sertkayahuseyin/Solar-Panel-Tracking-the-Sun-with-Two-Axis-Motion/Media/Images/1.jpg

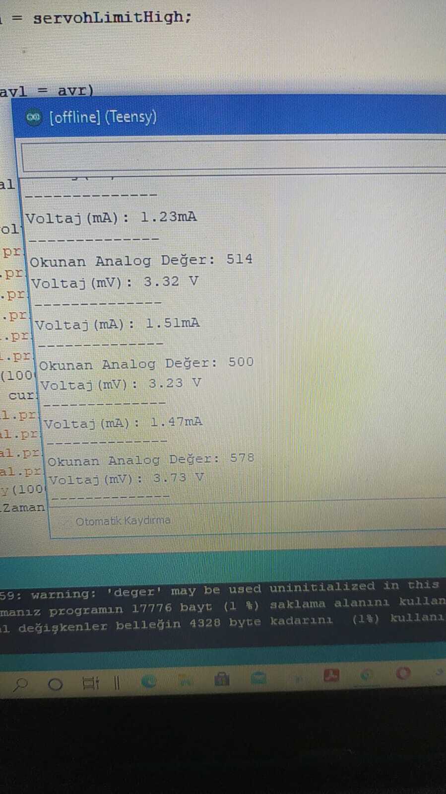
Media/Images/1.jpg
