sertkayahuseyin/Solar-Panel-Tracking-the-Sun-with-Two-Axis-Motion/Media/Images/2.jpg

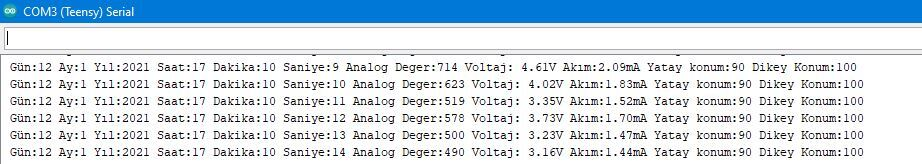
Media/Images/2.jpg
