sertkayahuseyin/Solar-Panel-Tracking-the-Sun-with-Two-Axis-Motion/Media/Images/4.jpg

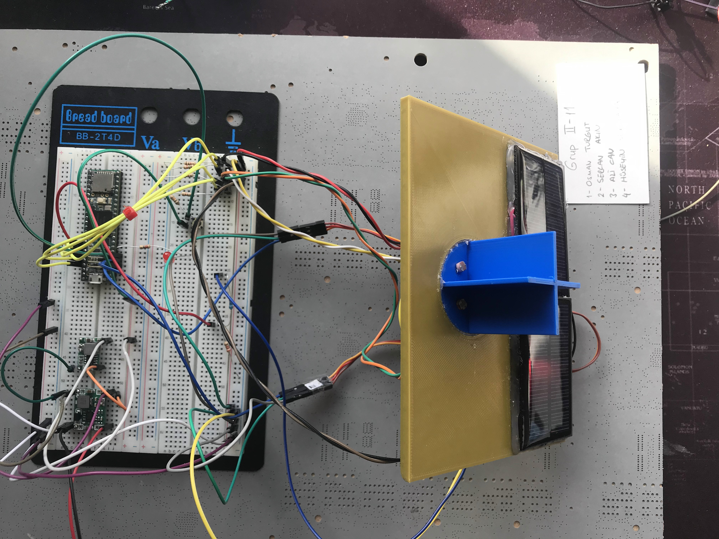
Media/Images/4.jpg
