sertkayahuseyin/Solar-Panel-Tracking-the-Sun-with-Two-Axis-Motion/Media/Images/6.jpg

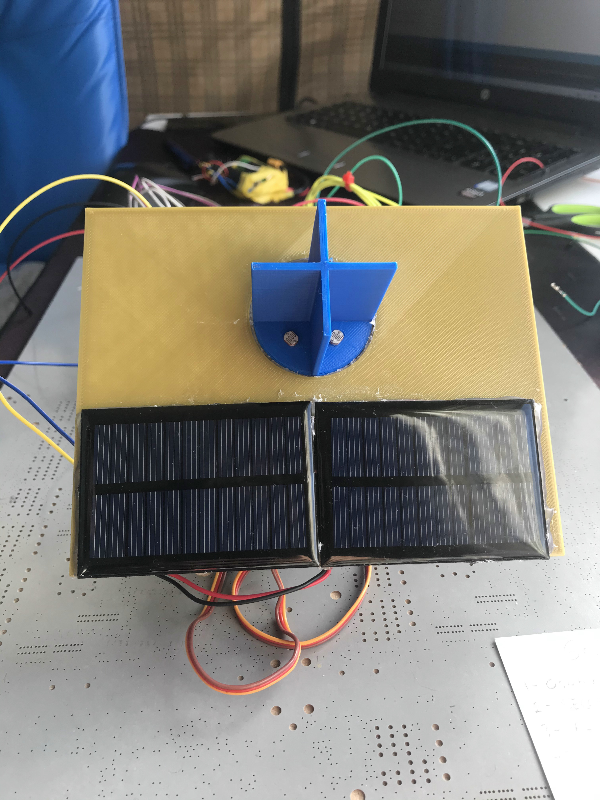
Media/Images/6.jpg
