sertkayahuseyin/Solar-Panel-Tracking-the-Sun-with-Two-Axis-Motion/Media/Images/7.jpg

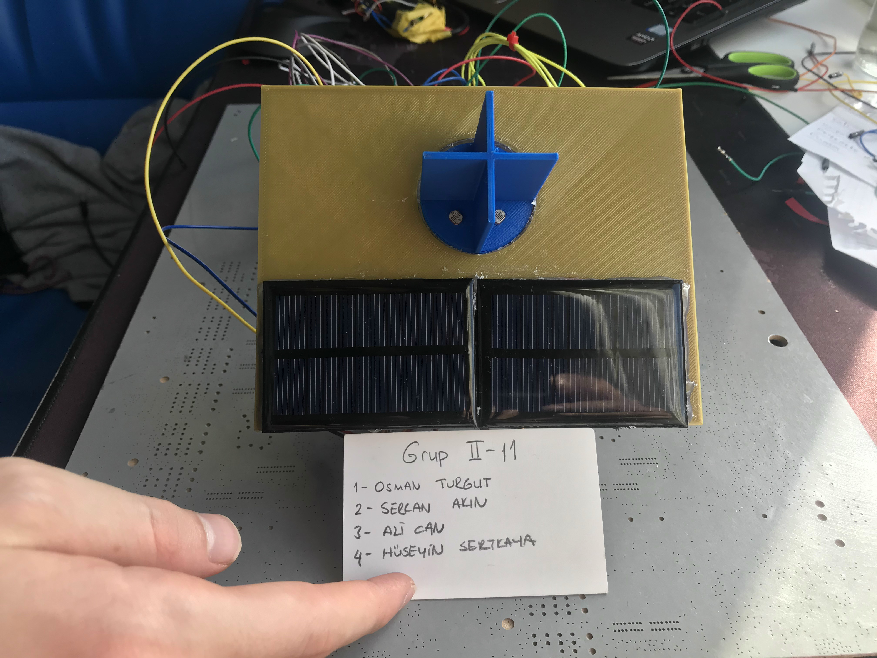
Media/Images/7.jpg
