sertkayahuseyin/Solar-Panel-Tracking-the-Sun-with-Two-Axis-Motion/Media/Images/10.jpeg

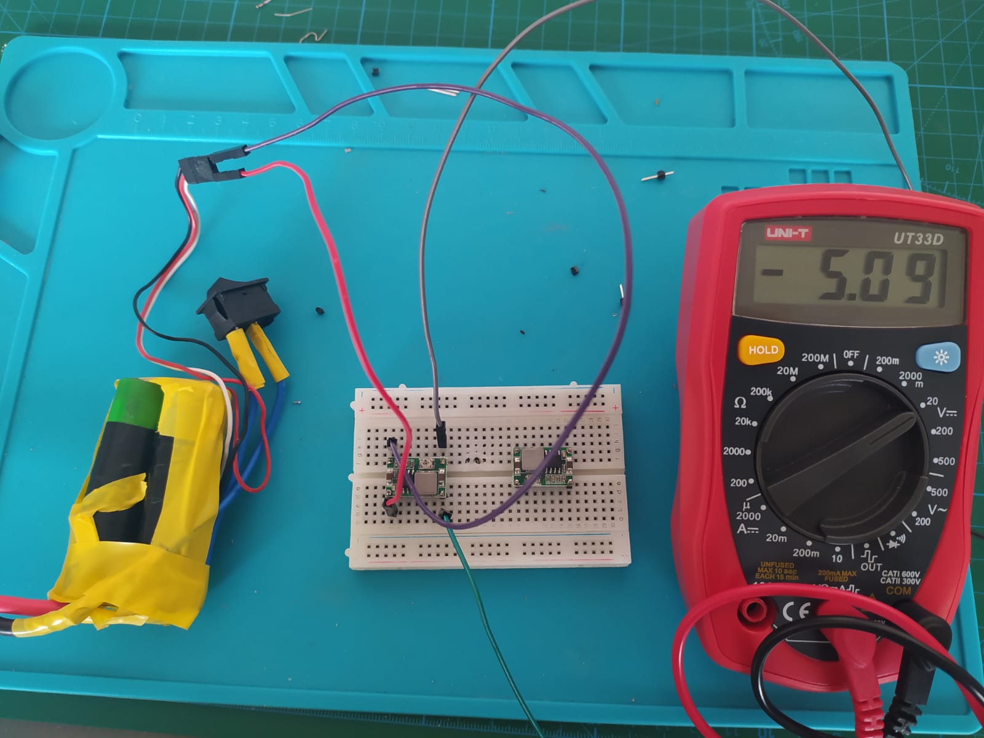
Media/Images/10.jpeg
