sertkayahuseyin/Solar-Panel-Tracking-the-Sun-with-Two-Axis-Motion/Media/Images/11.jpeg

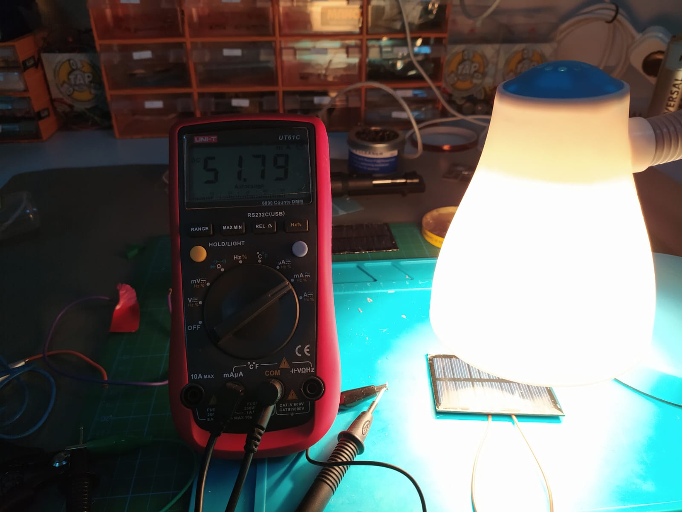
Media/Images/11.jpeg
